SpottedIonut/TSC-Proiect/TSC/USBLC6-2SC6Y.stp

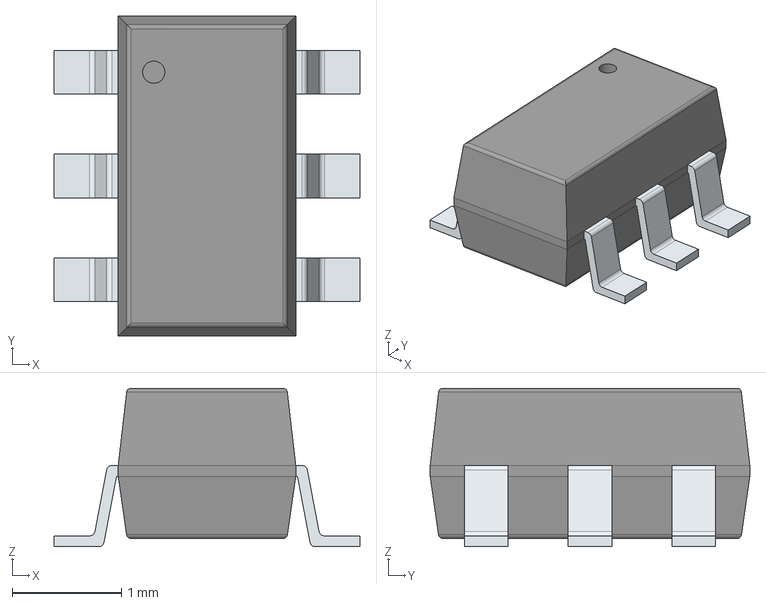
[picture p15: CAD file, 2025-04-06]
TSC/USBLC6-2SC6Y.stp
2.80 x 2.92 x 1.45 mm
PinsArrayLR
