SpottedIonut/TSC-Proiect/TSC/Resistor_0402.step

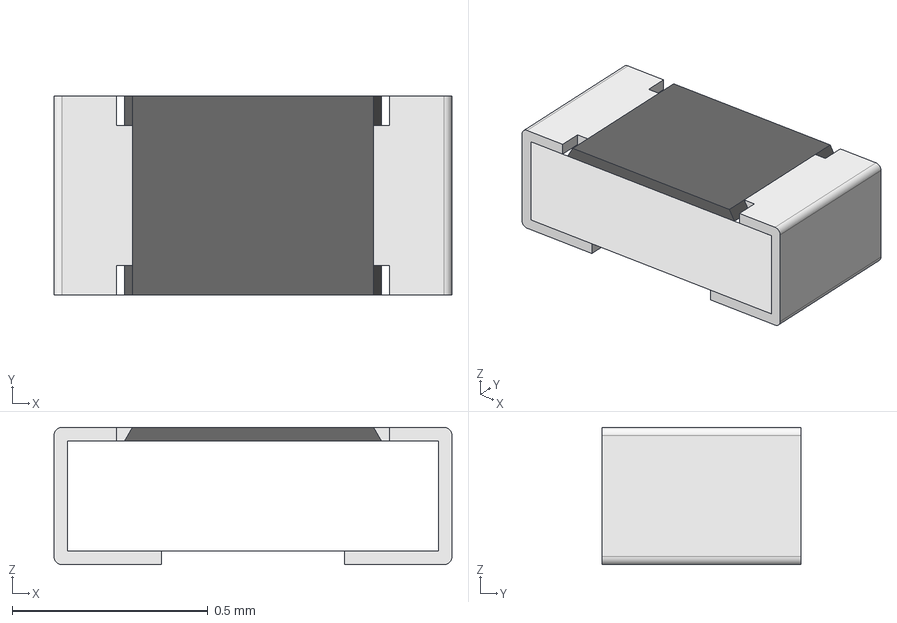
[picture p16: CAD file, 2025-04-06]
TSC/Resistor_0402.step
1.02 x 0.508 x 0.35 mm
Pin1
Pin2
CeramicBody
Coating
