SpottedIonut/TSC-Proiect/TSC/PRT-14417.stp

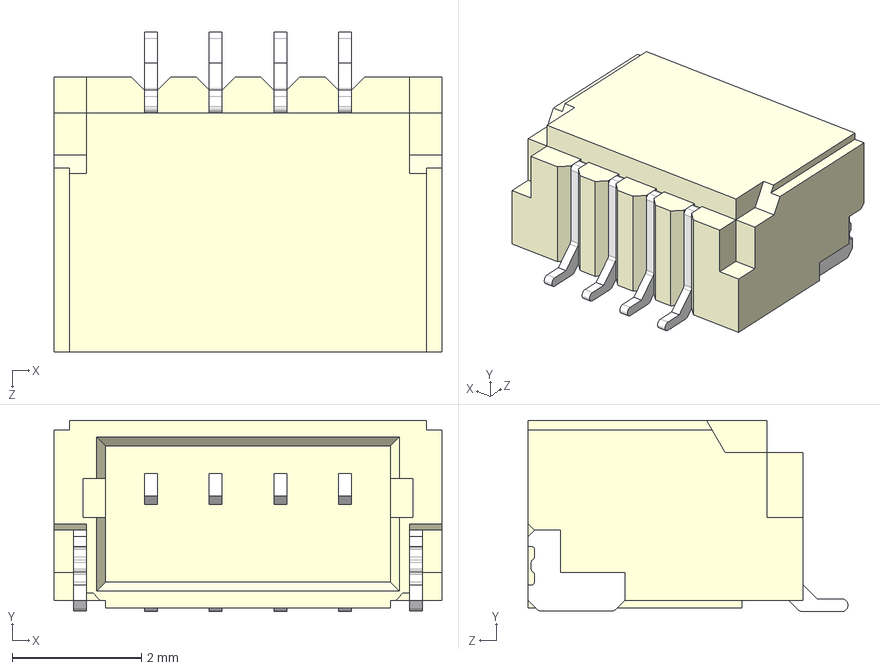
[picture p17: CAD file, 2025-04-06]
TSC/PRT-14417.stp
6.00 x 2.96 x 4.95 mm
