SpottedIonut/TSC-Proiect/TSC/FH34SRJ-24S-0.5SH_99_.stp

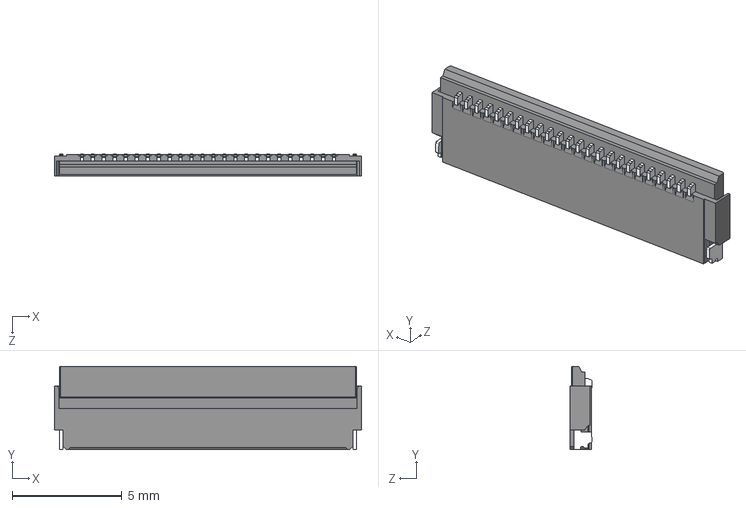
[picture p18: CAD file, 2025-04-06]
TSC/FH34SRJ-24S-0.5SH_99_.stp
14.0 x 3.80 x 1.00 mm
