SpottedIonut/TSC-Proiect/TSC/MBR0530.STEP

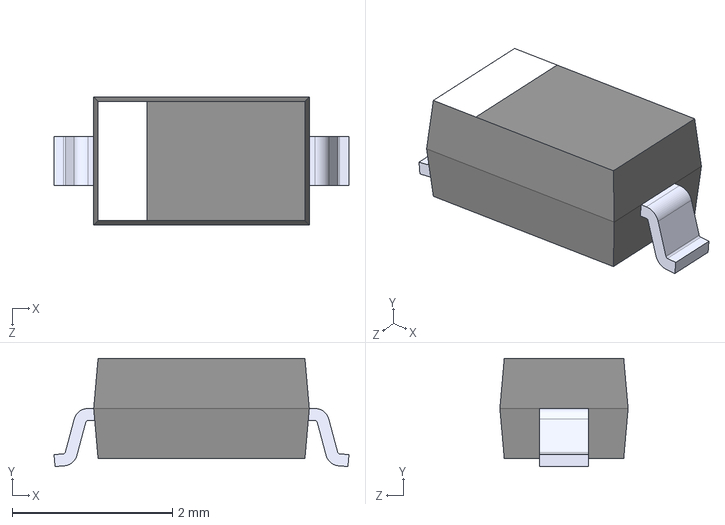
[picture p19: CAD file, 2025-04-06]
TSC/MBR0530.STEP
3.68 x 1.35 x 1.60 mm
